OLIMEX/LoRa-STM32WL-DevKIT/HARDWARE/LoRa-STM32WL-DevKIT/LoRa-STM32WL-DevKit-RevD1/3d/usb_micro_4p.stp

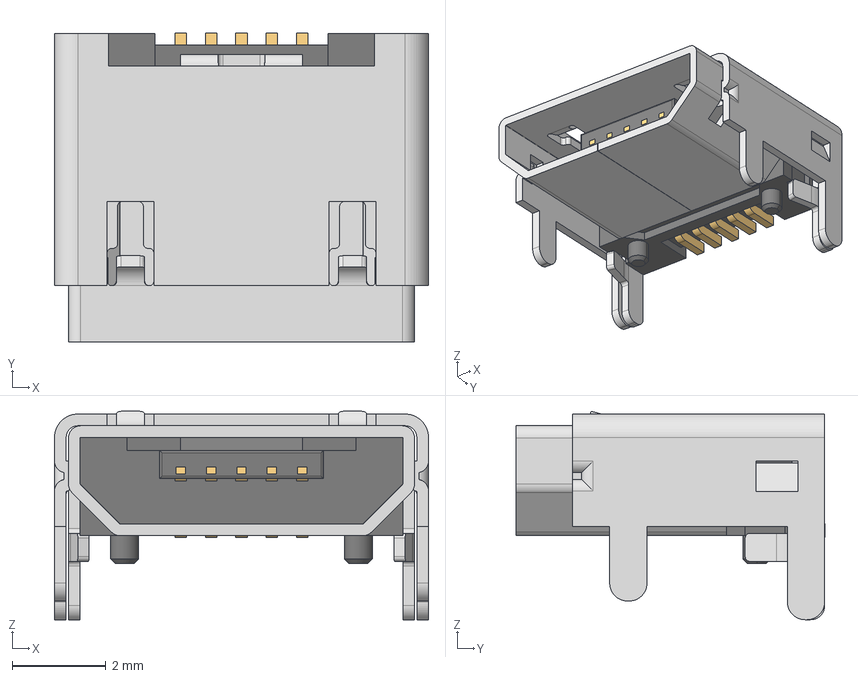
[picture p15: CAD file, 2023-03-29]
HARDWARE/LoRa-STM32WL-DevKIT/LoRa-STM32WL-DevKit-RevD1/3d/usb_micro_4p.stp
8.00 x 6.60 x 4.46 mm
