OLIMEX/LoRa-STM32WL-DevKIT/HARDWARE/LoRa-STM32WL-DevKIT/LoRa-STM32WL-DevKit-RevB/3d/BAT_1xAA_HOLDER.step

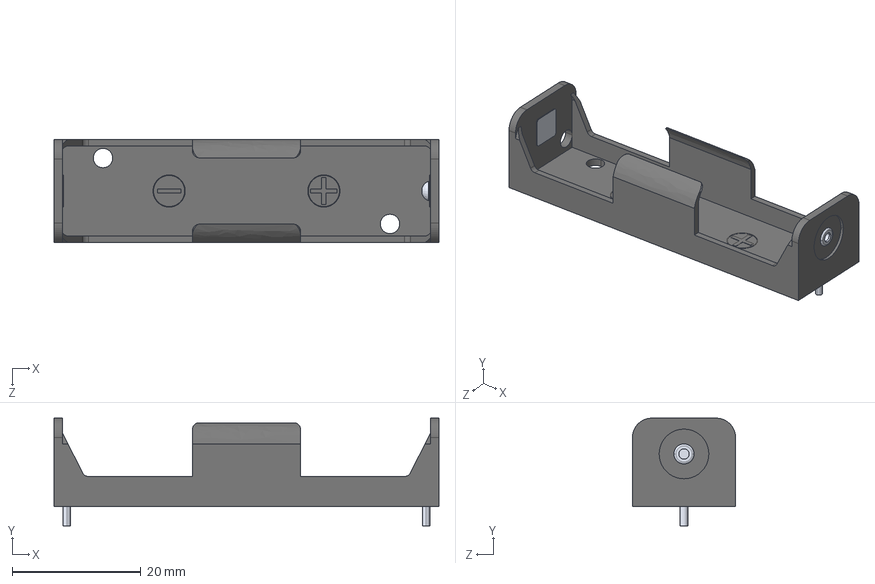
[picture p16: CAD file, 2023-03-29]
HARDWARE/LoRa-STM32WL-DevKIT/LoRa-STM32WL-DevKit-RevB/3d/BAT_1xAA_HOLDER.step
59.7 x 16.7 x 16.0 mm
