OLIMEX/LoRa-STM32WL-DevKIT/HARDWARE/LoRa-STM32WL-DevKIT/LoRa-STM32WL-DevKit-RevB/3d/HN1x2-PinHeader_1x02_P2.54mm_Vertical.step

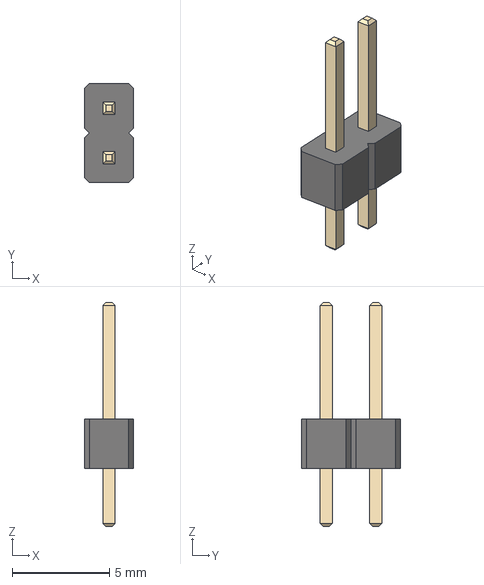
[picture p17: CAD file, 2021-11-23]
HARDWARE/LoRa-STM32WL-DevKIT/LoRa-STM32WL-DevKit-RevB/3d/HN1x2-PinHeader_1x02_P2.54mm_Vertical.step
2.54 x 5.08 x 11.5 mm
