OLIMEX/LoRa-STM32WL-DevKIT/HARDWARE/LoRa-STM32WL-DevKIT/LoRa-STM32WL-DevKit-RevD1/3d/HN1x10-PinHeader_1x10_P2.54mm_Vertical.step

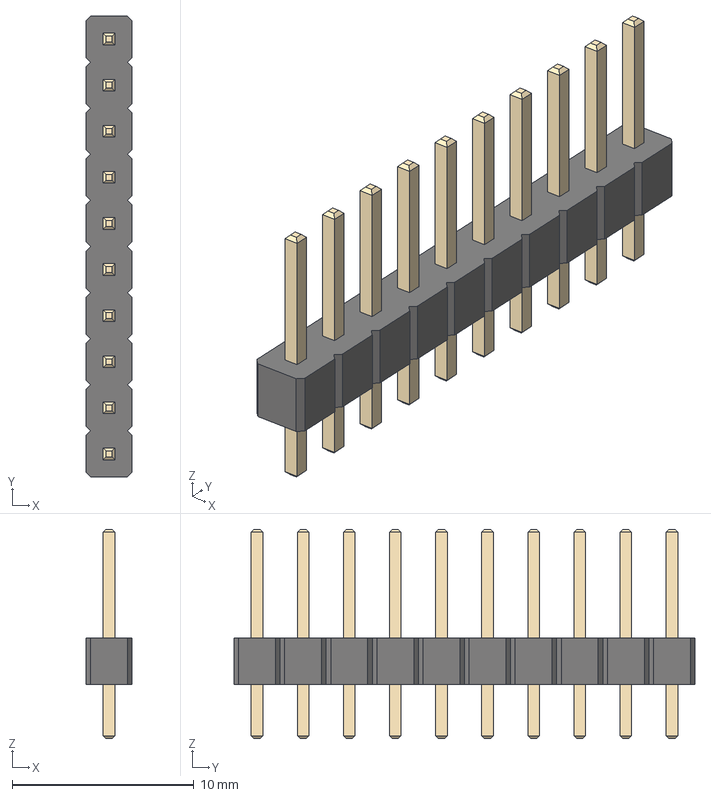
[picture p18: CAD file, 2021-11-23]
HARDWARE/LoRa-STM32WL-DevKIT/LoRa-STM32WL-DevKit-RevD1/3d/HN1x10-PinHeader_1x10_P2.54mm_Vertical.step
2.54 x 25.4 x 11.5 mm
