OLIMEX/LoRa-STM32WL-DevKIT/SOFTWARE/New-revision-demo/LoRaWAN/868/Core/Src/main.c

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
/* Includes ------------------------------------------------------------------*/
#include "main.h"
#include "app_lorawan.h"

/* USER CODE BEGIN Includes */
#include "sys_app.h"
/* USER CODE END Includes */

ADC_HandleTypeDef hadc;

RNG_HandleTypeDef hrng;

RTC_HandleTypeDef hrtc;

SUBGHZ_HandleTypeDef hsubghz;

UART_HandleTypeDef huart1;
DMA_HandleTypeDef hdma_usart1_tx;

/* USER CODE BEGIN PV */
uint8_t lse_available = 0;
/* USER CODE END PV */

void SystemClock_Config(void);
static void MX_GPIO_Init(void);
static void MX_RNG_Init(void);
/* USER CODE BEGIN 0 */

#define IIS2MDC_ADDR      0x1E
#define IIS2MDC_CFG_REG_A 0x60
#define IIS2MDC_CFG_REG_C 0x62
#define IIS2MDC_OUTX_L    0x68

#define AHT20_ADDR        0x38

static int I2C1_WaitFlag(uint32_t flag, uint32_t timeout_ms)
{
  uint32_t t = HAL_GetTick() + timeout_ms;
  while (!(I2C1->ISR & flag))
  {
    if (I2C1->ISR & I2C_ISR_NACKF)
    {
      I2C1->ICR = I2C_ICR_NACKCF;
      return -1;
    }
    if (HAL_GetTick() > t) return -1;
  }
  return 0;
}

static void I2C1_Init(void)
{
  __HAL_RCC_GPIOA_CLK_ENABLE();
  GPIO_InitTypeDef gpio = {0};
  gpio.Pin = GPIO_PIN_9 | GPIO_PIN_10;
  gpio.Mode = GPIO_MODE_AF_OD;
  gpio.Pull = GPIO_PULLUP;
  gpio.Speed = GPIO_SPEED_FREQ_LOW;
  gpio.Alternate = GPIO_AF4_I2C1;
  HAL_GPIO_Init(GPIOA, &gpio);

  __HAL_RCC_I2C1_CLK_ENABLE();
  I2C1->CR1 &= ~I2C_CR1_PE;
  I2C1->TIMINGR = 0x00707CBB;
  I2C1->OAR1 = 0;
  I2C1->OAR2 = 0;
  I2C1->CR1 = I2C_CR1_PE;
}

static int I2C1_WriteReg(uint8_t addr, uint8_t reg, uint8_t *data, uint16_t len)
{
  uint32_t t = HAL_GetTick() + 100;
  while (I2C1->ISR & I2C_ISR_BUSY) { if (HAL_GetTick() > t) return -1; }

  I2C1->CR2 = (addr << 1) | (((uint32_t)(len + 1)) << I2C_CR2_NBYTES_Pos)
              | I2C_CR2_AUTOEND | I2C_CR2_START;

  if (I2C1_WaitFlag(I2C_ISR_TXIS, 100) != 0) return -1;
  I2C1->TXDR = reg;

  for (uint16_t i = 0; i < len; i++)
  {
    if (I2C1_WaitFlag(I2C_ISR_TXIS, 100) != 0) return -1;
    I2C1->TXDR = data[i];
  }

  if (I2C1_WaitFlag(I2C_ISR_STOPF, 100) != 0) return -1;
  I2C1->ICR = I2C_ICR_STOPCF;
  return 0;
}

static int I2C1_ReadReg(uint8_t addr, uint8_t reg, uint8_t *data, uint16_t len)
{
  uint32_t t = HAL_GetTick() + 100;
  while (I2C1->ISR & I2C_ISR_BUSY) { if (HAL_GetTick() > t) return -1; }

  I2C1->CR2 = (addr << 1) | (1U << I2C_CR2_NBYTES_Pos) | I2C_CR2_START;
  if (I2C1_WaitFlag(I2C_ISR_TXIS, 100) != 0) return -1;
  I2C1->TXDR = reg;
  if (I2C1_WaitFlag(I2C_ISR_TC, 100) != 0) return -1;

  I2C1->CR2 = (addr << 1) | I2C_CR2_RD_WRN
              | (((uint32_t)len) << I2C_CR2_NBYTES_Pos)
              | I2C_CR2_AUTOEND | I2C_CR2_START;

  for (uint16_t i = 0; i < len; i++)
  {
    if (I2C1_WaitFlag(I2C_ISR_RXNE, 100) != 0) return -1;
    data[i] = (uint8_t)I2C1->RXDR;
  }

  if (I2C1_WaitFlag(I2C_ISR_STOPF, 100) != 0) return -1;
  I2C1->ICR = I2C_ICR_STOPCF;
  return 0;
}

static int I2C1_WriteBytes(uint8_t addr, uint8_t *data, uint16_t len)
{
  uint32_t t = HAL_GetTick() + 100;
  while (I2C1->ISR & I2C_ISR_BUSY) { if (HAL_GetTick() > t) return -1; }

  I2C1->CR2 = (addr << 1) | (((uint32_t)len) << I2C_CR2_NBYTES_Pos)
              | I2C_CR2_AUTOEND | I2C_CR2_START;

  for (uint16_t i = 0; i < len; i++)
  {
    if (I2C1_WaitFlag(I2C_ISR_TXIS, 100) != 0) return -1;
    I2C1->TXDR = data[i];
  }

  if (I2C1_WaitFlag(I2C_ISR_STOPF, 100) != 0) return -1;
  I2C1->ICR = I2C_ICR_STOPCF;
  return 0;
}

static int I2C1_ReadBytes(uint8_t addr, uint8_t *data, uint16_t len)
{
  uint32_t t = HAL_GetTick() + 100;
  while (I2C1->ISR & I2C_ISR_BUSY) { if (HAL_GetTick() > t) return -1; }

  I2C1->CR2 = (addr << 1) | I2C_CR2_RD_WRN
              | (((uint32_t)len) << I2C_CR2_NBYTES_Pos)
              | I2C_CR2_AUTOEND | I2C_CR2_START;

  for (uint16_t i = 0; i < len; i++)
  {
    if (I2C1_WaitFlag(I2C_ISR_RXNE, 100) != 0) return -1;
    data[i] = (uint8_t)I2C1->RXDR;
  }

  if (I2C1_WaitFlag(I2C_ISR_STOPF, 100) != 0) return -1;
  I2C1->ICR = I2C_ICR_STOPCF;
  return 0;
}

void IIS2MDC_Init(void)
{
  uint8_t val = 0x00;
  I2C1_WriteReg(IIS2MDC_ADDR, IIS2MDC_CFG_REG_A, &val, 1);
  val = 0x10;
  I2C1_WriteReg(IIS2MDC_ADDR, IIS2MDC_CFG_REG_C, &val, 1);
}

void IIS2MDC_Read(int16_t *x, int16_t *y, int16_t *z)
{
  uint8_t buf[6] = {0};
  I2C1_ReadReg(IIS2MDC_ADDR, IIS2MDC_OUTX_L, buf, 6);
  *x = (int16_t)((uint16_t)buf[1] << 8 | buf[0]);
  *y = (int16_t)((uint16_t)buf[3] << 8 | buf[2]);
  *z = (int16_t)((uint16_t)buf[5] << 8 | buf[4]);
}

void AHT20_Init(void)
{
  HAL_Delay(40);
  uint8_t cmd[3] = {0xBE, 0x08, 0x00};
  I2C1_WriteBytes(AHT20_ADDR, cmd, 3);
  HAL_Delay(10);
}

int16_t AHT20_ReadTemp_x10(void)
{
  uint8_t cmd[3] = {0xAC, 0x33, 0x00};
  I2C1_WriteBytes(AHT20_ADDR, cmd, 3);
  HAL_Delay(80);

  uint8_t data[7] = {0};
  I2C1_ReadBytes(AHT20_ADDR, data, 7);
  if (data[0] & 0x80)
  {
    HAL_Delay(80);
    I2C1_ReadBytes(AHT20_ADDR, data, 7);
  }

  uint32_t raw = ((uint32_t)(data[3] & 0x0F) << 16)
                 | ((uint32_t)data[4] << 8) | data[5];
  return (int16_t)((raw * 2000UL) / 1048576UL) - 500;
}

uint8_t LDR_ReadLevel(void)
{
  ADC_ChannelConfTypeDef sConfig = {0};
  MX_ADC_Init();
  if (HAL_ADCEx_Calibration_Start(&hadc) != HAL_OK) return 0;

  sConfig.Channel = ADC_CHANNEL_3;
  sConfig.Rank = ADC_REGULAR_RANK_1;
  sConfig.SamplingTime = ADC_SAMPLINGTIME_COMMON_1;
  if (HAL_ADC_ConfigChannel(&hadc, &sConfig) != HAL_OK) return 0;
  if (HAL_ADC_Start(&hadc) != HAL_OK) return 0;

  HAL_ADC_PollForConversion(&hadc, HAL_MAX_DELAY);
  HAL_ADC_Stop(&hadc);
  uint32_t raw = HAL_ADC_GetValue(&hadc);
  HAL_ADC_DeInit(&hadc);

  return (uint8_t)(raw * 100 / 4095);
}

uint8_t Button_IsPressed(void)
{
  return (HAL_GPIO_ReadPin(GPIOA, GPIO_PIN_0) == GPIO_PIN_RESET) ? 1 : 0;
}

/* USER CODE END 0 */

/**
  * @brief  The application entry point.
  * @retval int
  */
int main(void)
{

  /* MCU Configuration--------------------------------------------------------*/

  /* Reset of all peripherals, Initializes the Flash interface and the Systick. */
  HAL_Init();

  /* Configure the system clock */
  SystemClock_Config();

  /* Initialize all configured peripherals */
  MX_GPIO_Init();
  MX_DMA_Init();
  MX_ADC_Init();
  MX_RNG_Init();
  MX_RTC_Init();
  MX_USART1_UART_Init();
  MX_SUBGHZ_Init();
  MX_LoRaWAN_Init();
  /* USER CODE BEGIN 2 */
  I2C1_Init();
  IIS2MDC_Init();
  AHT20_Init();
  APP_LOG(TS_OFF, VLEVEL_L, "Sensors initialized (IIS2MDC, AHT20, Button, LDR)\r\n");
  /* USER CODE END 2 */

  /* Infinite loop */
  /* USER CODE BEGIN WHILE */
  while (1)
  {
    /* USER CODE END WHILE */
    MX_LoRaWAN_Process();

    /* USER CODE BEGIN 3 */
  }
  /* USER CODE END 3 */
}

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
