OLIMEX/LoRa-STM32WL-DevKIT/SOFTWARE/New-revision-demo/LoRaWAN/868/Core/Inc/main.h

#define RTC_N_PREDIV_S 8 /* PREDIV_A=127 fixed by HAL in binary-only mode -> 32768/128=256Hz -> 2^8=256 */
#define RTC_PREDIV_S ((1<<RTC_N_PREDIV_S)-1)
#define RTC_PREDIV_A ((1<<(15-RTC_N_PREDIV_S))-1)
#define FE_CTRL2_Pin GPIO_PIN_8
#define FE_CTRL2_GPIO_Port GPIOB
#define FE_CTRL1_Pin GPIO_PIN_13
#define FE_CTRL1_GPIO_Port GPIOC
