OLIMEX/LoRa-STM32WL-DevKIT/SOFTWARE/New-revision-demo/LoRaWAN/868/Core/Inc/sys_conf.h

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

/* Define to prevent recursive inclusion -------------------------------------*/
#ifndef __SYS_CONF_H__
#define __SYS_CONF_H__

#ifdef __cplusplus
extern "C" {
#endif

/* Includes ------------------------------------------------------------------*/
/* Exported types ------------------------------------------------------------*/
/* Exported constants --------------------------------------------------------*/

/**
  * @brief Temperature and pressure values are retrieved from sensors shield
  *        (instead of sending dummy values). It requires MEMS IKS shield
  */
#define SENSOR_ENABLED                       0

/**
  * @brief  Verbose level for all trace logs
  */
#define VERBOSE_LEVEL                        VLEVEL_L

/**
  * @brief Enable trace logs
  */
#define APP_LOG_ENABLED                      1

/**
  * @brief Activate monitoring (probes) of some internal RF signals for debug purpose
  */
#define DEBUG_SUBGHZSPI_MONITORING_ENABLED   0

#define DEBUG_RF_NRESET_ENABLED              0

#define DEBUG_RF_HSE32RDY_ENABLED            0

#define DEBUG_RF_SMPSRDY_ENABLED             0

#define DEBUG_RF_LDORDY_ENABLED              0

#define DEBUG_RF_DTB1_ENABLED                0

#define DEBUG_RF_BUSY_ENABLED                0

/**
  * @brief Enable/Disable MCU Debugger pins (dbg serial wires)
  * @note  by HW serial wires are ON by default, need to put them OFF to save power
  */
#define DEBUGGER_ENABLED                     0

/**
  * @brief Disable Low Power mode
  * @note  0: LowPowerMode enabled. MCU enters stop2 mode, 1: LowPowerMode disabled. MCU enters sleep mode only
  */
#define LOW_POWER_DISABLE                    1

/* External variables --------------------------------------------------------*/
/* Exported macro ------------------------------------------------------------*/
/* Exported functions prototypes ---------------------------------------------*/
#ifdef __cplusplus
}
#endif

#endif /* __SYS_CONF_H__ */
